oddsocks1024/b5s4-XA1541-Active/images/3.jpg

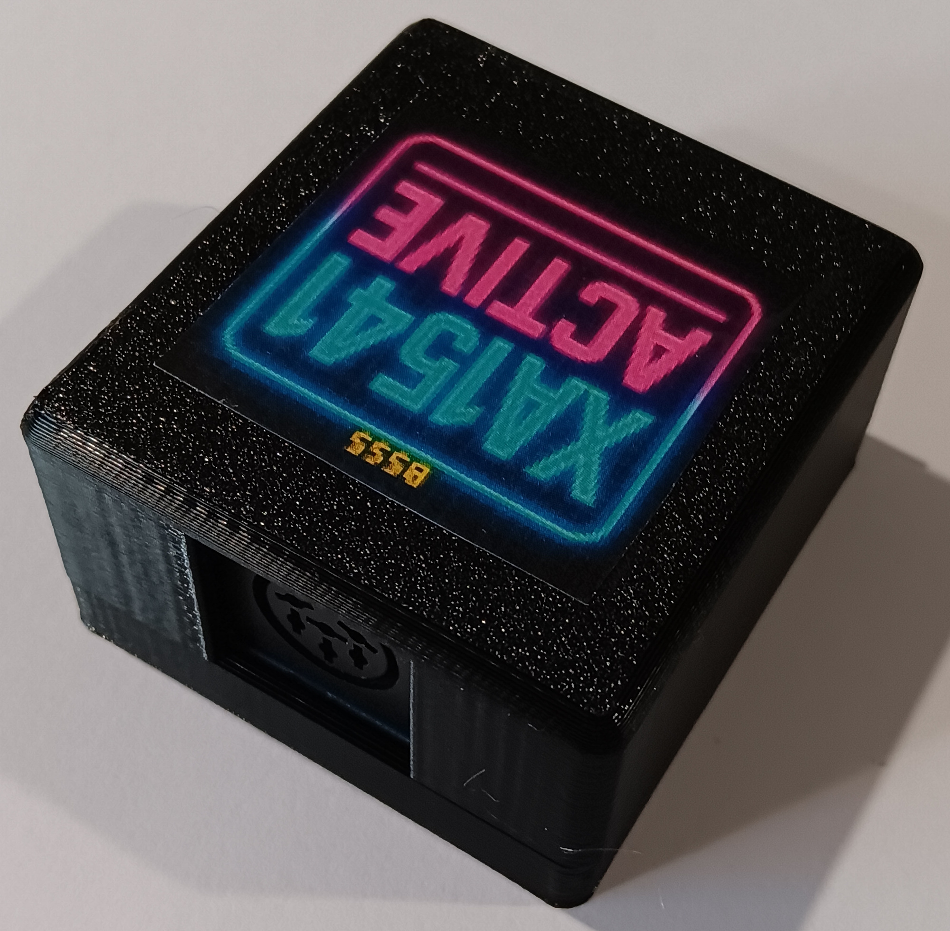
images/3.jpg
